mcweihing/crkbd-4x6/pictures/20190530_102304.jpg

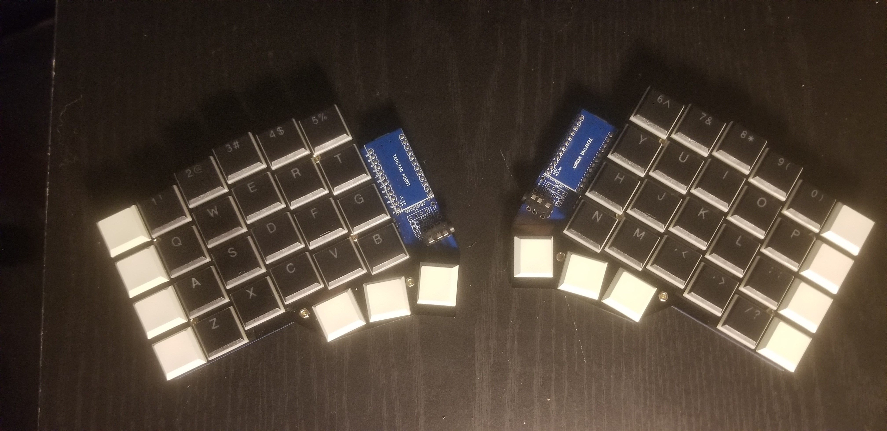
pictures/20190530_102304.jpg
